rahim974/2526_projet1a_pcbot1/Test_nRF24_recepteur/Core/Inc/main.h

#define B1_Pin GPIO_PIN_13
#define B1_GPIO_Port GPIOC
#define USART_TX_Pin GPIO_PIN_2
#define USART_TX_GPIO_Port GPIOA
#define USART_RX_Pin GPIO_PIN_3
#define USART_RX_GPIO_Port GPIOA
#define NRF_CE_Pin GPIO_PIN_7
#define NRF_CE_GPIO_Port GPIOC
#define NRF_IRQ_Pin GPIO_PIN_9
#define NRF_IRQ_GPIO_Port GPIOA
#define TMS_Pin GPIO_PIN_13
#define TMS_GPIO_Port GPIOA
#define TCK_Pin GPIO_PIN_14
#define TCK_GPIO_Port GPIOA
#define SWO_Pin GPIO_PIN_3
#define SWO_GPIO_Port GPIOB
#define NRF_CSN_Pin GPIO_PIN_6
#define NRF_CSN_GPIO_Port GPIOB
